AymenBerrafaa/AMR-PFE-2026/Photos/WhatsApp Image 2026-04-14 at 8.51.28 PM (2).jpeg

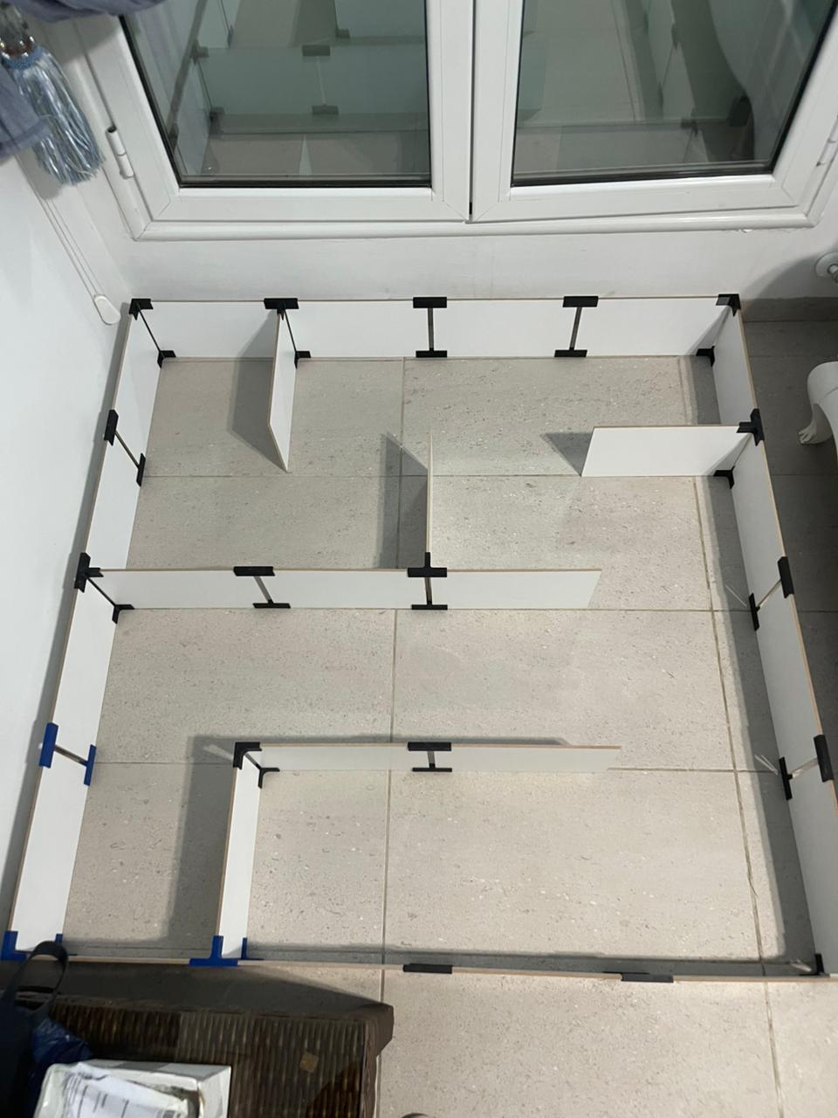
Photos/WhatsApp Image 2026-04-14 at 8.51.28 PM (2).jpeg
