AymenBerrafaa/AMR-PFE-2026/Photos/WhatsApp Image 2026-05-14 at 3.01.14 PM (1).jpeg

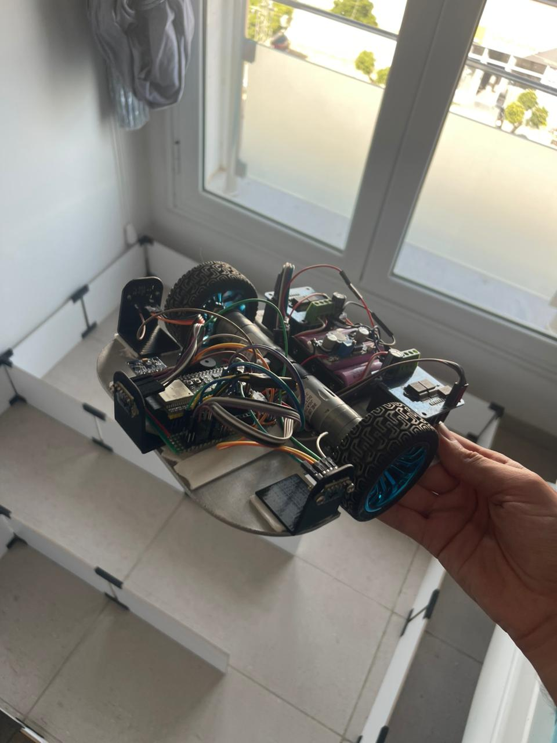
Photos/WhatsApp Image 2026-05-14 at 3.01.14 PM (1).jpeg
