AymenBerrafaa/AMR-PFE-2026/Photos/WhatsApp Image 2026-05-14 at 3.01.15 PM.jpeg

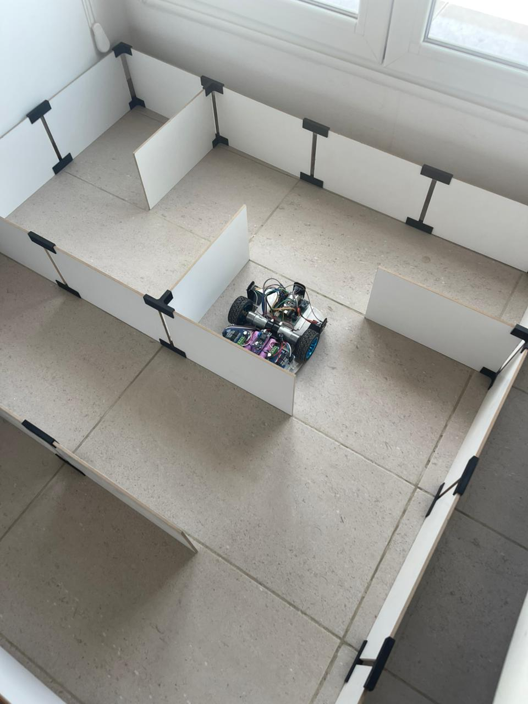
Photos/WhatsApp Image 2026-05-14 at 3.01.15 PM.jpeg
