AymenBerrafaa/AMR-PFE-2026/Photos/WhatsApp Image 2026-05-19 at 1.59.03 PM.jpeg

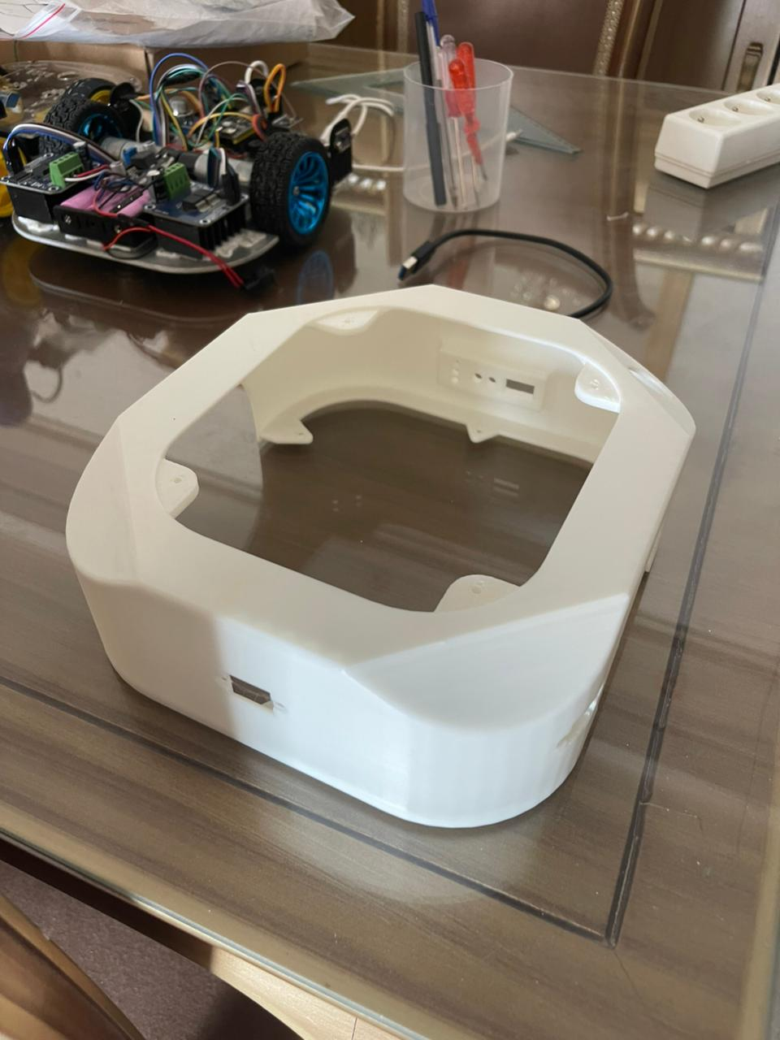
Photos/WhatsApp Image 2026-05-19 at 1.59.03 PM.jpeg
