AymenBerrafaa/AMR-PFE-2026/Photos/WhatsApp Image 2026-05-19 at 1.59.04 PM (2).jpeg

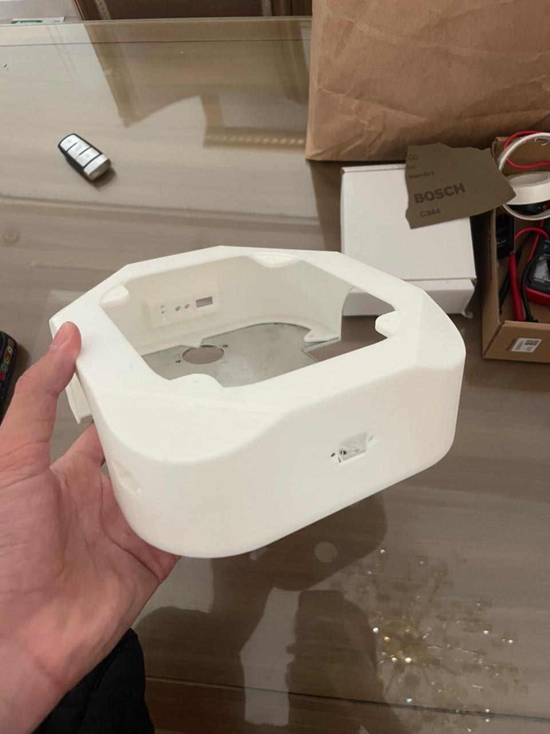
Photos/WhatsApp Image 2026-05-19 at 1.59.04 PM (2).jpeg
