AymenBerrafaa/AMR-PFE-2026/Photos/WhatsApp Image 2026-05-21 at 2.42.39 PM.jpeg

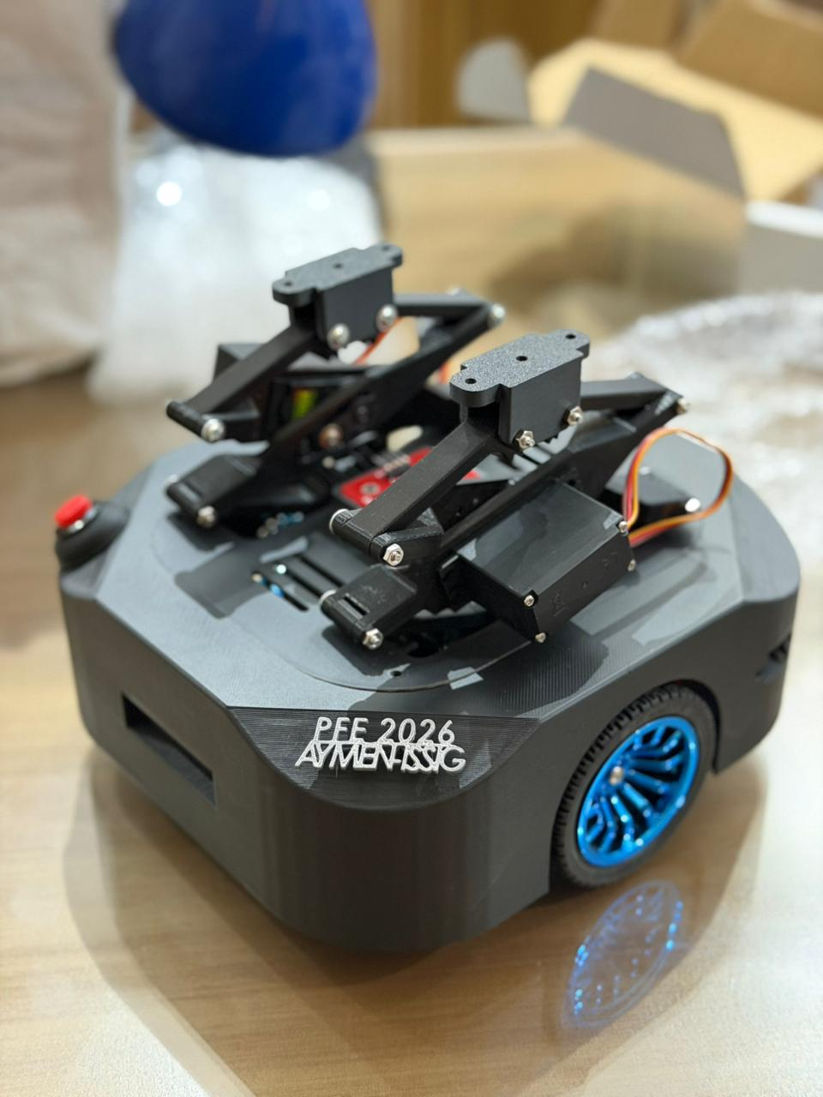
Photos/WhatsApp Image 2026-05-21 at 2.42.39 PM.jpeg
