AymenBerrafaa/AMR-PFE-2026/Photos/WhatsApp Image 2026-05-26 at 2.25.29 PM (1).jpeg

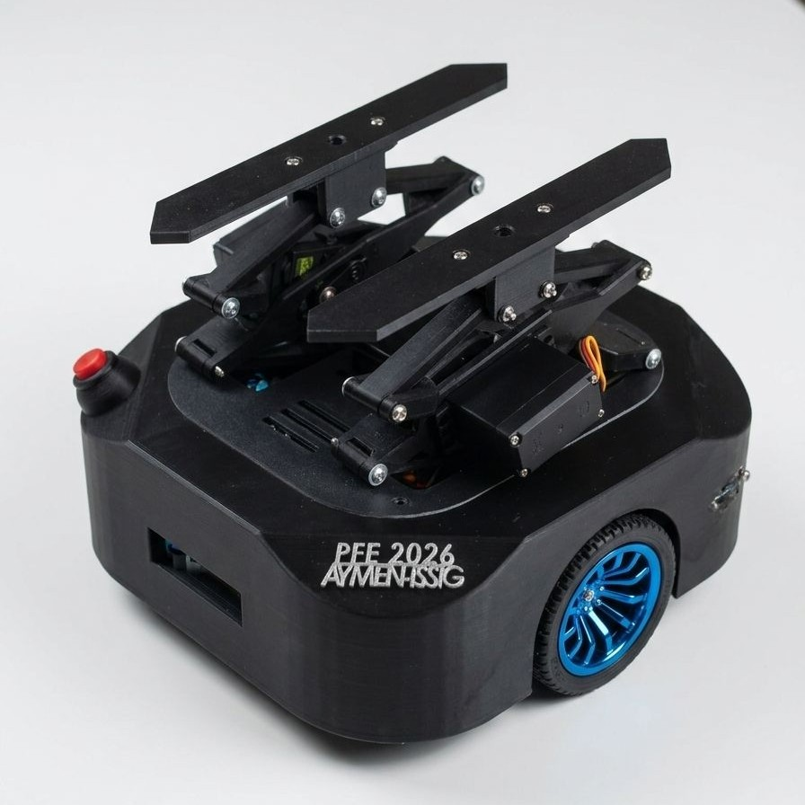
Photos/WhatsApp Image 2026-05-26 at 2.25.29 PM (1).jpeg
