AymenBerrafaa/AMR-PFE-2026/Photos/WhatsApp Image 2026-05-26 at 2.25.30 PM (2).jpeg

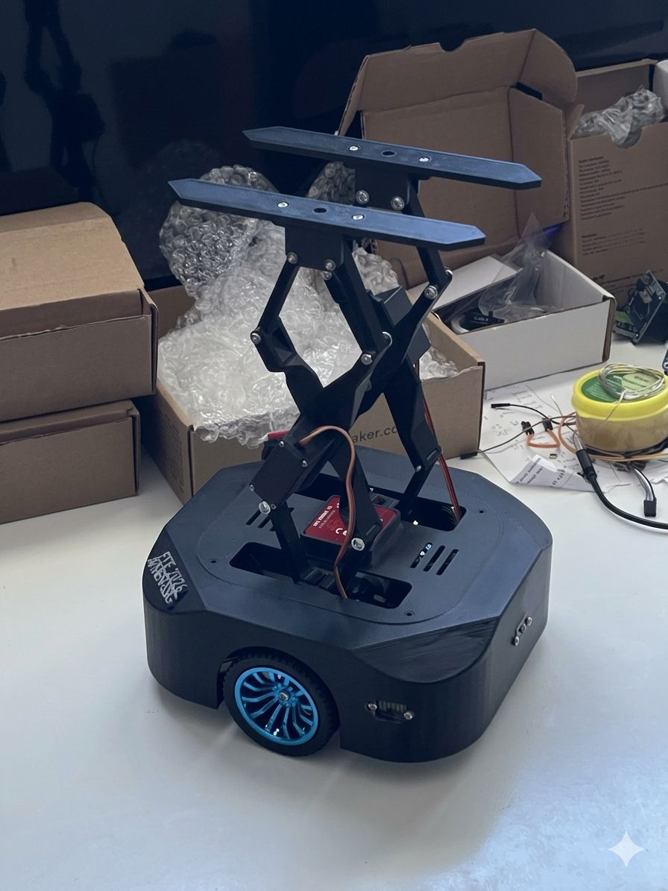
Photos/WhatsApp Image 2026-05-26 at 2.25.30 PM (2).jpeg
