AymenBerrafaa/AMR-PFE-2026/Photos/WhatsApp Image 2026-05-26 at 2.25.34 PM.jpeg

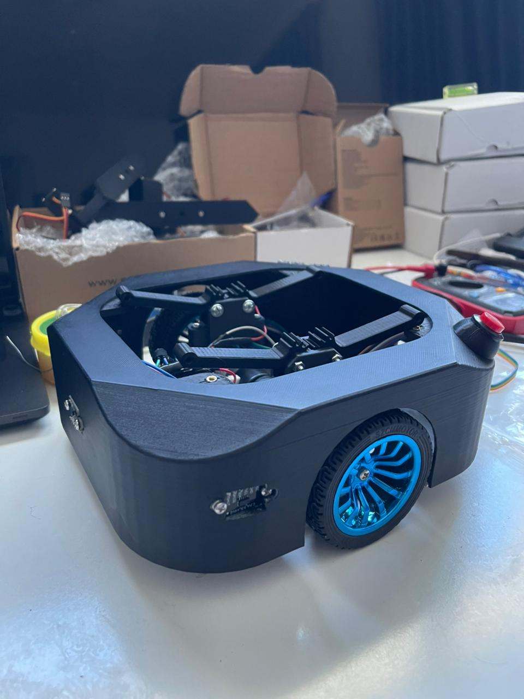
Photos/WhatsApp Image 2026-05-26 at 2.25.34 PM.jpeg
