AymenBerrafaa/AMR-PFE-2026/Photos/WhatsApp Image 2026-05-26 at 4.40.33 PM.jpeg

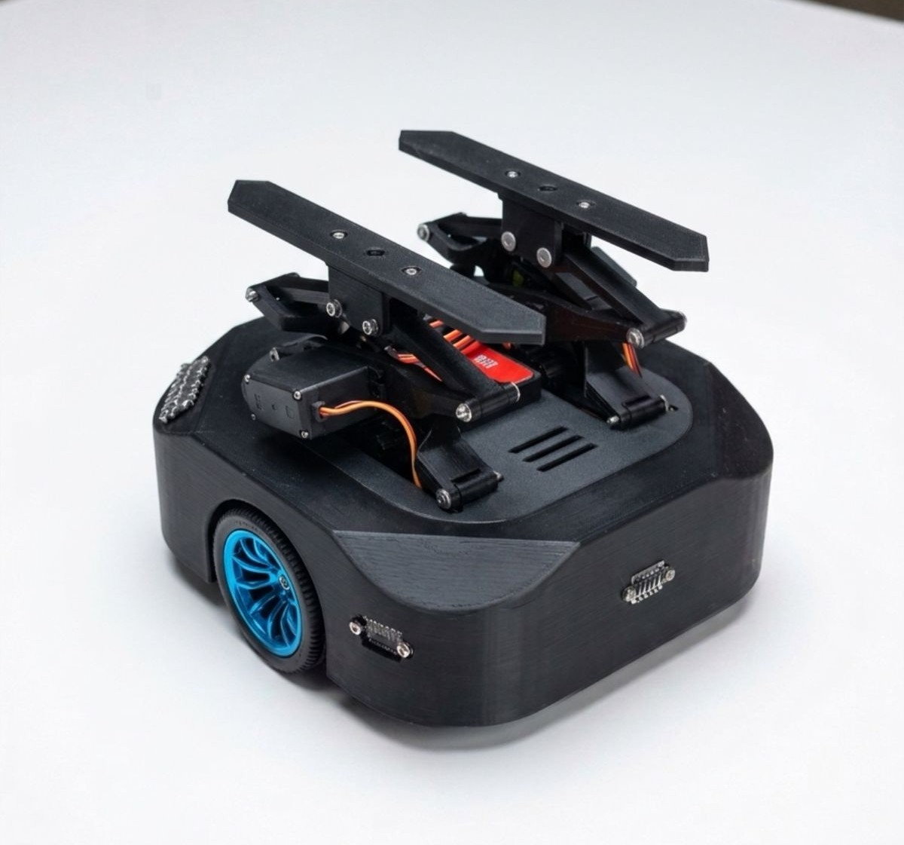
Photos/WhatsApp Image 2026-05-26 at 4.40.33 PM.jpeg
